andrewwdao/MIS-Locker/docs/pictures/Konel.png

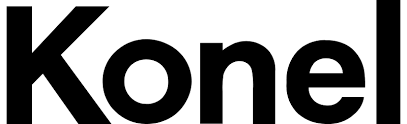
docs/pictures/Konel.png
