andrewwdao/MIS-Locker/docs/pictures/lcd01.jpg

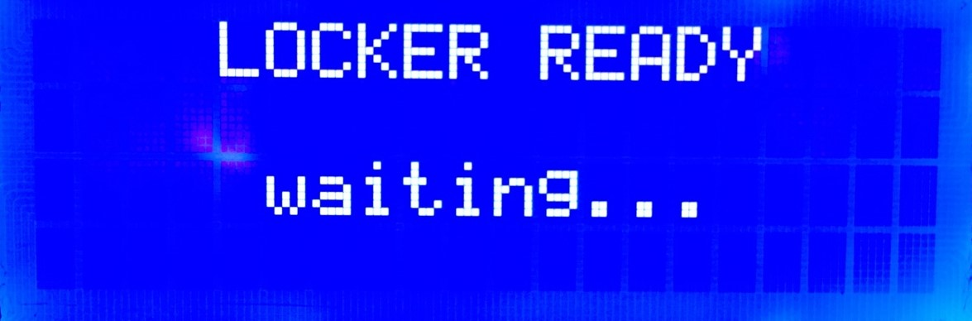
docs/pictures/lcd01.jpg
