andrewwdao/MIS-Locker/docs/pictures/lcd04.jpg

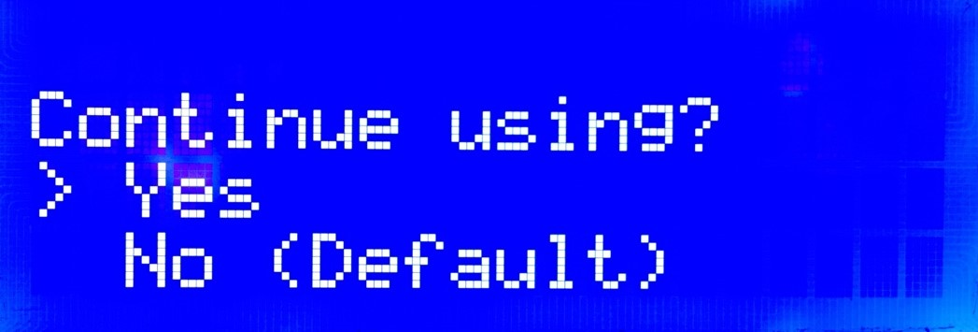
docs/pictures/lcd04.jpg
