andrewwdao/MIS-Locker/docs/pictures/lcd05.jpg

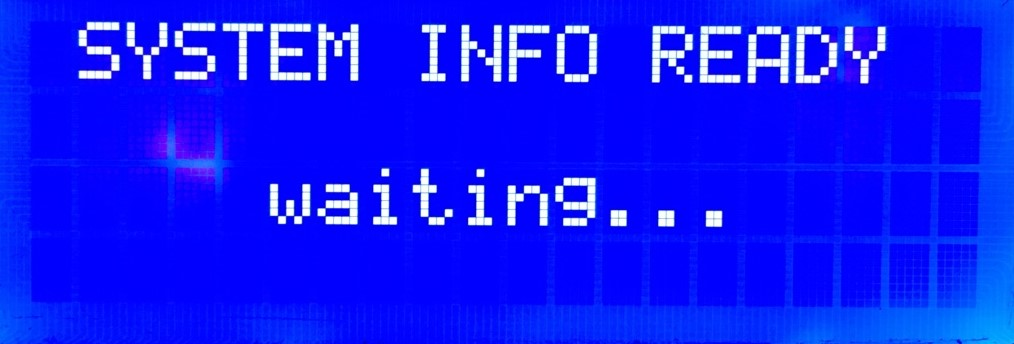
docs/pictures/lcd05.jpg
