andrewwdao/MIS-Locker/docs/pictures/lcd06.jpg

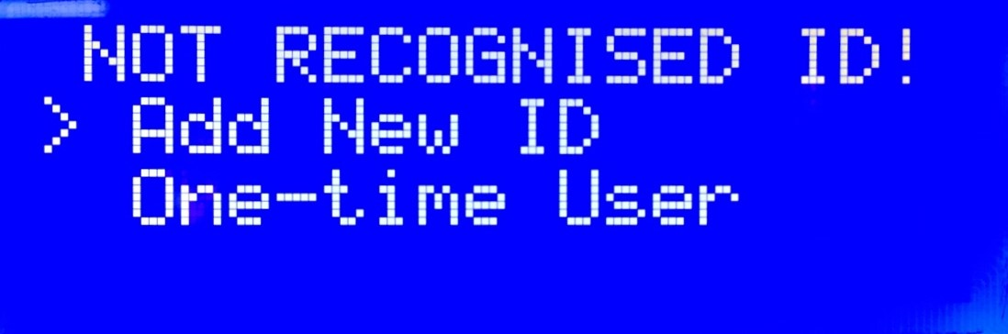
docs/pictures/lcd06.jpg
