andrewwdao/MIS-Locker/docs/pictures/noise_filter.jpg

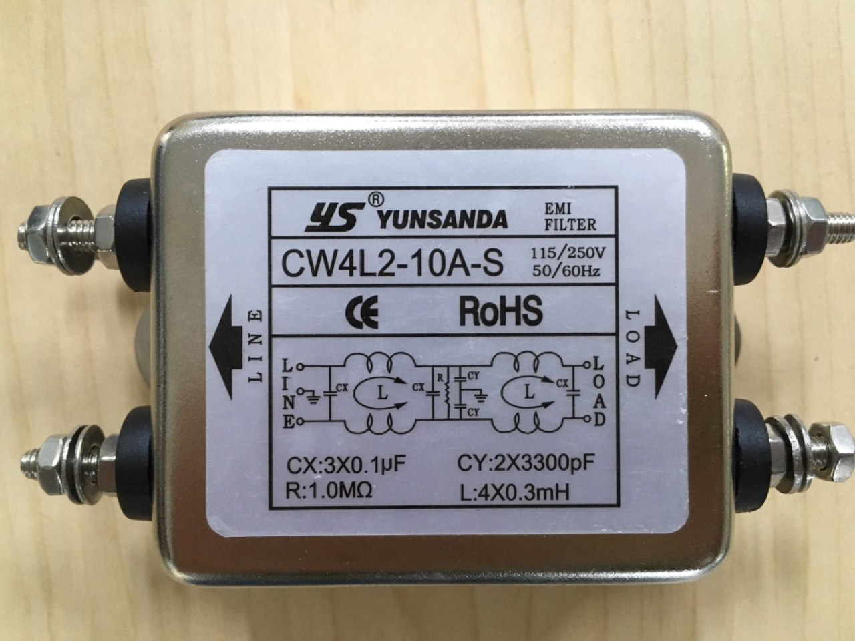
docs/pictures/noise_filter.jpg
