andrewwdao/MIS-Locker/components/Fingerprint/fingerPrint.py

"""------------------------------------------------------------*-
  fingerPrint module for Raspberry Pi
  Tested on: Raspberry Pi 3 B+
  (c) Minh-An Dao 2019
  (C) Bastian Raschke 2015
  version 1.00 - 09/10/2019
 --------------------------------------------------------------
 *
 *
 --------------------------------------------------------------"""
from pyfingerprint.pyfingerprint import PyFingerprint
import RPi.GPIO as GPIO  # default as BCM mode!
import time
from datetime import datetime
import button  # for the cancel button

# ---------------------------- Private Parameters:
# -----Starting parameter:
FINGER_PORT = '/dev/ttyUSB0'
FINGER_BAUDRATE = 57600
FINGER_ADDRESS = 0xFFFFFFFF
FINGER_PASSWORD = 0x00000000
TOUCH_PIN = 4  # BCM Mode
WAIT_TIME = 5  # waiting time between first and second scan of enroll func
DEBOUNCE = 10
START_CHECKING = False
Finger = None
# button.init() # already been done in main.py
positionNumber = int()
# ------------------------------ Basic functions ------------------------------
def begin():  # Tries to initialize the sensor
    global Finger
    try:
        # pulled up to avoid false detection.
        # So we'll be setting up falling edge detection
        GPIO.setmode(GPIO.BCM)
        GPIO.setup(TOUCH_PIN, GPIO.IN, pull_up_down=GPIO.PUD_UP)
        Finger = PyFingerprint(FINGER_PORT, FINGER_BAUDRATE, FINGER_ADDRESS, FINGER_PASSWORD)
        if not Finger.verifyPassword():
            raise ValueError('Password for the Fingerprint module is wrong!')
        # Gets some sensor information
        print('Fingerprint used templates: ' + str(Finger.getTemplateCount()) + '/' + str(Finger.getStorageCapacity()))
        return True
    except Exception as e:
        print('The fingerprint sensor could not be initialized!')
        print('Exception message: ' + str(e))
        return False


def __scan():  # Search for the incoming finger in database, DO NOT do this all the time since it will reduce the lifetime of the sensor --> the reason for the existance of the ISR
    try:
        global positionNumber
        last_millis = datetime.now().second
        print('Waiting for finger...')
        while not Finger.readImage():  # Wait for incoming finger is read
            # only wait for WAIT_TIME seconds
            if (datetime.now().second - last_millis) > WAIT_TIME:
                return "NO DATA"
            # pass

        # Converts read image to characteristics and stores it in charbuffer 1
        Finger.convertImage(0x01)

        # Search for template info in the database of the R301T
        result = Finger.searchTemplate()
        positionNumber = result[0]
        accuracyScore = result[1]

        if positionNumber == -1:
            print('No match found!')
            print("NOT MATCHED")
            return "NOT MATCHED"
        else:
            print('Template found at #' + str(positionNumber))
            print('Accuracy: ' + str(accuracyScore))
            print("MATCHED. Position Number: "+ str(positionNumber))
            return "MATCHED"
    except Exception as e:
        print('Operation failed!')
        print('Exception message: ' + str(e))
        print("ERROR")
        return "ERROR"


def __touchISR(channel):
    global START_CHECKING
    START_CHECKING = True

def user_position():
    return positionNumber

def activate():
    GPIO.add_event_detect(TOUCH_PIN, GPIO.FALLING, callback=__touchISR, bouncetime=DEBOUNCE)


def deactivate():
    GPIO.remove_event_detect(TOUCH_PIN)


def check():
    global START_CHECKING
    if START_CHECKING:
        START_CHECKING = False
        return __scan()
    return "NO DATA"


def flush():
    global START_CHECKING
    START_CHECKING = False


def first_enroll():
    try:
        print('Waiting for finger...')
        while not Finger.readImage():  # Wait for incoming finger is read
            if button.read() is "BUT_CANCEL":
                return ["CANCEL", 0]
            # pass

        # Converts read image to characteristics and stores it in charbuffer 1
        Finger.convertImage(0x01)

        # Checks if finger is already enrolled
        result = Finger.searchTemplate()
        positionNumber = result[0]
        if positionNumber >= 0:
            # NEED TO ADD ALGORITHM HERE
            print('Finger already exists at #' + str(positionNumber))
            return ["EXISTED", positionNumber]

        print('First enroll done.')
        return ["DONE",0]
    except Exception as e:
        print('Operation failed!')
        print('Exception message: ' + str(e))
        return ["ERROR", e]


def second_enroll():
    try:
        print('Second time. Waiting for finger...')

        while not Finger.readImage():  # Wait that finger is read again
            if button.read() is "BUT_CANCEL":
                return ["CANCEL", 0]
            # pass

        # Converts read image to characteristics and stores it in charbuffer 2
        Finger.convertImage(0x02)

        # Compares the charbuffers
        if not Finger.compareCharacteristics():
            return ["FAILED", 0]

        # Pass second read. Creates the corresponding template
        Finger.createTemplate()

        # Saves the template at a new position number
        positionNumber = Finger.storeTemplate()
        print('Finger enrolled successfully!')
        print('New template position #' + str(positionNumber))
        return ["DONE", positionNumber]
    except Exception as e:
        print('Operation failed!')
        print('Exception message: ' + str(e))
        return ["ERROR", e]


def delete(pos):  # Delete the template of the finger
    try:
        if Finger.deleteTemplate(pos):
            print('Template deleted!')
            return True
    except Exception as e:
        print('Operation failed!')
        print('Exception message: ' + str(e))
        return False


def deleteAll():  # Delete all of the templates
    try:
        if Finger.clearDatabase():
            print('All Templates deleted!')
            return True
    except Exception as e:
        print('Operation failed!')
        print('Exception message: ' + str(e))
        return False
