andrewwdao/MIS-Locker/seperate_components/ADC_I2C/main_adc.py

from adc import adc_button,adc_switches
import time
button = adc_button()
switches = adc_switches()
while True:
    # print(switches.readRawM1())
    #print(switches.read())
    print(button.readRaw())
    #print(button.read())
    time.sleep(1)
